plb500/AutoBloomer-SensorModule/hardware/HIB/PCB/HardwareInterfaceBoard.kicad_sch

## KiCad design hardware/HIB/PCB/HardwareInterfaceBoard.kicad_sch (2024-02-22)

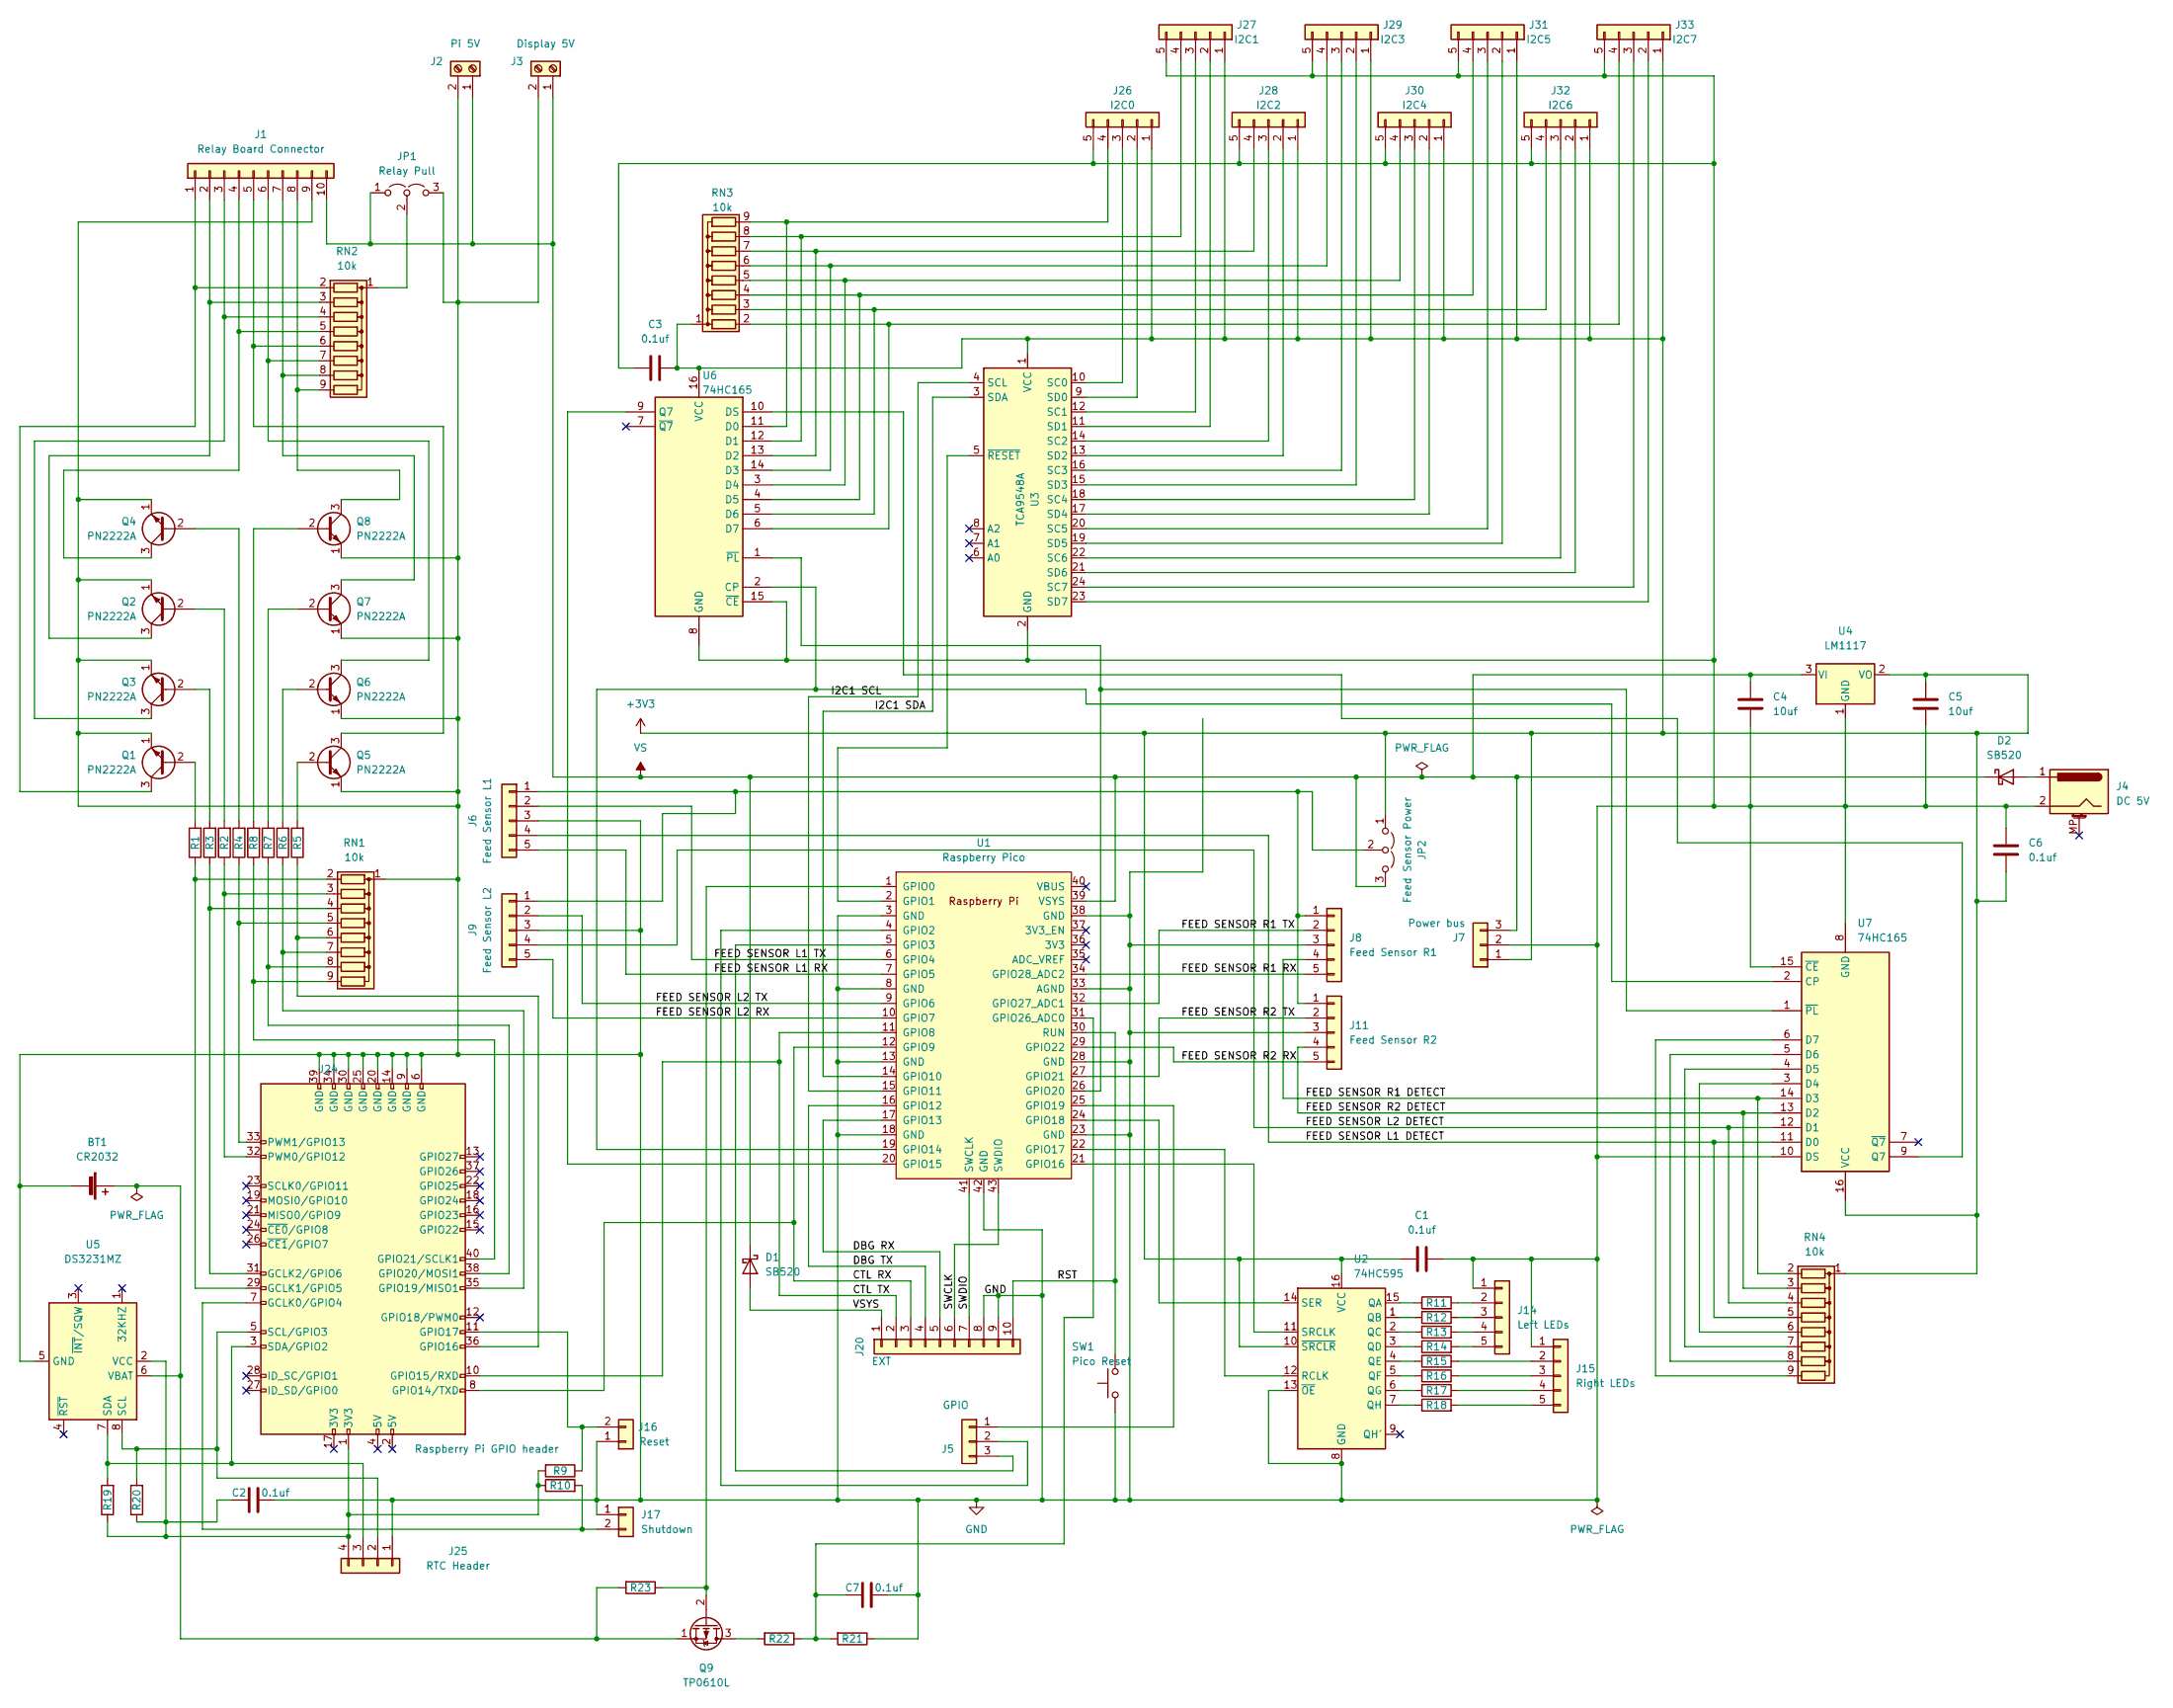
[picture p12: schematic HardwareInterfaceBoard.kicad_sch]

Parts:
BT1: CR2032; BatteryHolder_Keystone_1058_1x2032
C1, C2, C3, C6, C7: 0.1uf; C_Disc_D6.0mm_W2.5mm_P5.00mm
C4, C5: 10uf; C_Disc_D6.0mm_W2.5mm_P5.00mm
D1, D2: SB520; D_DO-201AD_P15.24mm_Horizontal
J1: Relay Board Connector; JST_XH_B10B-XH-A_1x10_P2.50mm_Vertical
J2: Pi 5V; JST_XH_B2B-XH-A_1x02_P2.50mm_Vertical
J3: Display 5V; JST_XH_B2B-XH-A_1x02_P2.50mm_Vertical
J4: DC 5V; BarrelJack_Horizontal_MP
J5: GPIO; PinHeader_1x03_P2.54mm_Vertical
J6: Feed Sensor L1; JST_XH_B5B-XH-A_1x05_P2.50mm_Vertical
J7: Power bus; PinHeader_1x03_P2.54mm_Vertical
J8: Feed Sensor R1; JST_XH_B5B-XH-A_1x05_P2.50mm_Vertical
J9: Feed Sensor L2; JST_XH_B5B-XH-A_1x05_P2.50mm_Vertical
J11: Feed Sensor R2; JST_XH_B5B-XH-A_1x05_P2.50mm_Vertical
J14: Left LEDs; JST_XH_B5B-XH-A_1x05_P2.50mm_Vertical
J15: Right LEDs; JST_XH_B5B-XH-A_1x05_P2.50mm_Vertical
J16: Reset; JST_XH_B2B-XH-A_1x02_P2.50mm_Vertical
J17: Shutdown; JST_XH_B2B-XH-A_1x02_P2.50mm_Vertical
J20: EXT; JST_XH_B10B-XH-A_1x10_P2.50mm_Vertical
J24: Raspberry Pi GPIO header; PinHeader_2x20_P2.54mm_Vertical
J25: RTC Header; PinHeader_1x04_P2.54mm_Vertical
J26: I2C0; JST_XH_B5B-XH-A_1x05_P2.50mm_Vertical
J27: I2C1; JST_XH_B5B-XH-A_1x05_P2.50mm_Vertical
J28: I2C2; JST_XH_B5B-XH-A_1x05_P2.50mm_Vertical
J29: I2C3; JST_XH_B5B-XH-A_1x05_P2.50mm_Vertical
J30: I2C4; JST_XH_B5B-XH-A_1x05_P2.50mm_Vertical
J31: I2C5; JST_XH_B5B-XH-A_1x05_P2.50mm_Vertical
J32: I2C6; JST_XH_B5B-XH-A_1x05_P2.50mm_Vertical
J33: I2C7; JST_XH_B5B-XH-A_1x05_P2.50mm_Vertical
JP1: Relay Pull; PinHeader_1x03_P2.54mm_Vertical
JP2: Feed Sensor Power; PinHeader_1x03_P2.54mm_Vertical
Q1, Q2, Q3, Q4, Q5, Q6, Q7, Q8: PN2222A; TO-92_Inline
Q9: TP0610L; TO-92_Inline
R1, R2, R3, R4, R5, R6, R7, R8: 2.2k; R_Axial_DIN0207_L6.3mm_D2.5mm_P7.62mm_Horizontal
R9, R10: 10k; R_Axial_DIN0207_L6.3mm_D2.5mm_P7.62mm_Horizontal
R11, R12, R13, R14, R15, R16, R17, R18: 300; R_Axial_DIN0207_L6.3mm_D2.5mm_P7.62mm_Horizontal
R19, R20: 4.3k; R_Axial_DIN0207_L6.3mm_D2.5mm_P7.62mm_Horizontal
R21, R22, R23: 100k; R_Axial_DIN0207_L6.3mm_D2.5mm_P7.62mm_Horizontal
RN1, RN2, RN3, RN4: 10k; R_Array_SIP9
SW1: Pico Reset; SW_PUSH_6mm
U1: Raspberry Pico; RPi_PicoW_SMD_TH
U2: 74HC595; DIP-16_W7.62mm
U3: TCA9548A; DIP-24_W15.24mm
U4: LM1117; TO-220-3_Horizontal_TabDown
U5: DS3231MZ; SOIC-8_3.9x4.9mm_P1.27mm
U6, U7: 74HC165; DIP-16_W7.62mm

Connections:
+3V3: C1.1, C3.1, C5.1, C6.2, J7.1, J26.1, J27.1, J28.1, J29.1, J30.1, J31.1, J32.1, J33.1, JP2.1 (A), RN3.1 (common), RN4.1 (common), U2.10 (~SRCLR), U2.16 (VCC), U3.1 (VCC), U4.2 (VO), U6.16 (VCC), U7.16 (VCC)
CTL RX: J20.3, J24.8 (GPIO14/TXD), U1.12 (GPIO9)
CTL TX: J20.2, J24.10 (GPIO15/RXD), U1.11 (GPIO8)
DBG RX: J20.5, U1.17 (GPIO13)
DBG TX: J20.4, U1.16 (GPIO12)
FEED SENSOR L1 DETECT: J6.4, RN4.5 (R4), U7.11 (D0)
FEED SENSOR L1 RX: J6.5, U1.7 (GPIO5)
FEED SENSOR L1 TX: J6.2, U1.6 (GPIO4)
FEED SENSOR L2 DETECT: J9.4, RN4.4 (R3), U7.12 (D1)
FEED SENSOR L2 RX: J9.5, U1.10 (GPIO7)
FEED SENSOR L2 TX: J9.2, U1.9 (GPIO6)
FEED SENSOR R1 DETECT: J8.4, RN4.2 (R1), U7.14 (D3)
FEED SENSOR R1 RX: J8.5, U1.34 (GPIO28_ADC2)
FEED SENSOR R1 TX: J8.2, U1.32 (GPIO27_ADC1)
FEED SENSOR R2 DETECT: J11.4, RN4.3 (R2), U7.13 (D2)
FEED SENSOR R2 RX: J11.5, U1.29 (GPIO22)
FEED SENSOR R2 TX: J11.2, U1.27 (GPIO21)
GND: BT1.2 (-), C1.2, C2.2, C3.2, C4.1, C5.2, C6.1, C7.2, J1.9, J2.2, J3.2, J4.2, J6.3, J7.2, J8.3, J9.3, J11.3, J14.1, J15.1, J16.1, J17.1, J20.8, J20.9, J24.6 (GND), J24.9 (GND), J24.14 (GND), J24.20 (GND), J24.25 (GND), J24.30 (GND), J24.34 (GND), J24.39 (GND), J25.1, J26.5, J27.5, J28.5, J29.5, J30.5, J31.5, J32.5, J33.5, JP1.3 (B), Q1.1 (E), Q2.1 (E), Q3.1 (E), Q4.1 (E), Q5.1 (E), Q6.1 (E), Q7.1 (E), Q8.1 (E), R21.1, RN1.1 (common), SW1.1, U1.3 (GND), U1.8 (GND), U1.13 (GND), U1.18 (GND), U1.23 (GND), U1.28 (GND), U1.33 (AGND), U1.38 (GND), U1.42 (GND), U2.8 (GND), U2.13 (~OE), U3.2 (GND), U4.1 (GND), U5.5 (GND), U6.8 (GND), U6.15 (~CE), U7.8 (GND), U7.10 (DS), U7.15 (~CE)
I2C1 SCL: U1.15 (GPIO11), U3.4 (SCL)
I2C1 SDA: U1.14 (GPIO10), U3.3 (SDA)
unnamed: BT1.1 (+), Q9.1 (S), R23.2, U5.6 (VBAT)
unnamed: C2.1, J24.1 (3V3), J25.4, R9.2, R10.1, R19.1, R20.1, U5.2 (VCC)
unnamed: C7.1, R21.2, R22.1, U1.31 (GPIO26_ADC0)
unnamed: D2.2 (A), J4.1
unnamed: J1.1, Q1.3 (C), RN2.2 (R1)
unnamed: J1.2, Q2.3 (C), RN2.3 (R2)
unnamed: J1.3, Q3.3 (C), RN2.4 (R3)
unnamed: J1.4, Q4.3 (C), RN2.5 (R4)
unnamed: J1.5, Q5.3 (C), RN2.6 (R5)
unnamed: J1.6, Q6.3 (C), RN2.7 (R6)
unnamed: J1.7, Q7.3 (C), RN2.8 (R7)
unnamed: J1.8, Q8.3 (C), RN2.9 (R8)
unnamed: J5.1, U1.25 (GPIO19)
unnamed: J5.2, U1.4 (GPIO2)
unnamed: J5.3, U1.5 (GPIO3)
unnamed: J6.1, J8.1, J9.1, J11.1, JP2.2 (C)
unnamed: J14.2, R11.2
unnamed: J14.3, R12.2
unnamed: J14.4, R13.2
unnamed: J14.5, R14.2
unnamed: J15.2, R15.2
unnamed: J15.3, R16.2
unnamed: J15.4, R17.2
unnamed: J15.5, R18.2
unnamed: J16.2, J24.11 (GPIO17), R9.1
unnamed: J17.2, J24.7 (GCLK0/GPIO4), R10.2
unnamed: J24.3 (SDA/GPIO2), J25.3, R19.2, U5.7 (SDA)
unnamed: J24.5 (SCL/GPIO3), J25.2, R20.2, U5.8 (SCL)
unnamed: J24.29 (GCLK1/GPIO5), R1.1, RN1.2 (R1)
unnamed: J24.31 (GCLK2/GPIO6), R3.1, RN1.4 (R3)
unnamed: J24.32 (PWM0/GPIO12), R2.1, RN1.3 (R2)
unnamed: J24.33 (PWM1/GPIO13), R4.1, RN1.5 (R4)
unnamed: J24.35 (GPIO19/MISO1), R6.1, RN1.7 (R6)
unnamed: J24.36 (GPIO16), R5.1, RN1.6 (R5)
unnamed: J24.38 (GPIO20/MOSI1), R7.1, RN1.8 (R7)
unnamed: J24.40 (GPIO21/SCLK1), R8.1, RN1.9 (R8)
unnamed: J26.2, U3.9 (SD0)
unnamed: J26.3, U3.10 (SC0)
unnamed: J26.4, RN3.9 (R8), U6.11 (D0)
unnamed: J27.2, U3.11 (SD1)
unnamed: J27.3, U3.12 (SC1)
unnamed: J27.4, RN3.8 (R7), U6.12 (D1)
unnamed: J28.2, U3.13 (SD2)
unnamed: J28.3, U3.14 (SC2)
unnamed: J28.4, RN3.7 (R6), U6.13 (D2)
unnamed: J29.2, U3.15 (SD3)
unnamed: J29.3, U3.16 (SC3)
unnamed: J29.4, RN3.6 (R5), U6.14 (D3)
unnamed: J30.2, U3.17 (SD4)
unnamed: J30.3, U3.18 (SC4)
unnamed: J30.4, RN3.5 (R4), U6.3 (D4)
unnamed: J31.2, U3.19 (SD5)
unnamed: J31.3, U3.20 (SC5)
unnamed: J31.4, RN3.4 (R3), U6.4 (D5)
unnamed: J32.2, U3.21 (SD6)
unnamed: J32.3, U3.22 (SC6)
unnamed: J32.4, RN3.3 (R2), U6.5 (D6)
unnamed: J33.2, U3.23 (SD7)
unnamed: J33.3, U3.24 (SC7)
unnamed: J33.4, RN3.2 (R1), U6.6 (D7)
unnamed: JP1.2 (C), RN2.1 (common)
unnamed: Q1.2 (B), R1.2
unnamed: Q2.2 (B), R2.2
unnamed: Q3.2 (B), R3.2
unnamed: Q4.2 (B), R4.2
unnamed: Q5.2 (B), R5.2
unnamed: Q6.2 (B), R6.2
unnamed: Q7.2 (B), R7.2
unnamed: Q8.2 (B), R8.2
unnamed: Q9.2 (G), R23.1, U1.1 (GPIO0)
unnamed: Q9.3 (D), R22.2
unnamed: R11.1, U2.15 (QA)
unnamed: R12.1, U2.1 (QB)
unnamed: R13.1, U2.2 (QC)
unnamed: R14.1, U2.3 (QD)
unnamed: R15.1, U2.4 (QE)
unnamed: R16.1, U2.5 (QF)
unnamed: R17.1, U2.6 (QG)
unnamed: R18.1, U2.7 (QH)
unnamed: RN4.6 (R5), U7.3 (D4)
unnamed: RN4.7 (R6), U7.4 (D5)
unnamed: RN4.8 (R7), U7.5 (D6)
unnamed: RN4.9 (R8), U7.6 (D7)
unnamed: U1.2 (GPIO1), U3.5 (~RESET)
unnamed: U1.19 (GPIO14), U6.2 (CP), U7.2 (CP)
unnamed: U1.20 (GPIO15), U6.9 (Q7)
unnamed: U1.21 (GPIO16), U2.11 (SRCLK)
unnamed: U1.22 (GPIO17), U2.12 (RCLK)
unnamed: U1.24 (GPIO18), U2.14 (SER)
unnamed: U1.26 (GPIO20), U6.1 (~PL), U7.1 (~PL)
unnamed: U6.10 (DS), U7.9 (Q7)
RST: J20.10, SW1.2, U1.30 (RUN)
SWCLK: J20.6, U1.43 (SWDIO)
SWDIO: J20.7, U1.41 (SWCLK)
VS: C4.2, D1.1 (K), D2.1 (K), J1.10, J2.1, J3.1, J7.3, JP1.1 (A), JP2.3 (B), U1.39 (VSYS), U4.3 (VI)
VSYS: D1.2 (A), J20.1
