plb500/AutoBloomer-SensorModule/pico/src/sensors/sensor_types/stemma_soil_sensor.cpp

#include "stemma_soil_sensor.h"

#include "util/debug_io.h"

#include <tuple>
#include <cstring>
#include <cstdio>


using std::make_tuple;

const uint8_t SEESAW_STATUS_BASE                = 0x00;
const uint8_t SEESAW_STATUS_HW_ID               = 0x01;
const uint8_t SEESAW_STATUS_SWRST               = 0x7F;
const uint8_t SEESAW_HW_ID_CODE                 = 0x55;
const uint8_t SEESAW_STATUS_VERSION             = 0x02;
const uint8_t SEESAW_TOUCH_BASE                 = 0x0F;
const uint8_t SEESAW_TOUCH_CHANNEL_OFFSET       = 0x10;

constexpr const char* SOIL_MOISTURE_JSON_KEY    = "SoilMoisture";


StemmaSoilSensor::StemmaSoilSensor(I2CInterface& i2cInterface, uint8_t address) :
    Sensor(Sensor::STEMMA_SOIL_SENSOR, &StemmaSoilSensor::serializeDataToJSON),
    mI2CInterface(i2cInterface),
    mAddress(address),
    mActive(false)
{}

void StemmaSoilSensor::doInitialization() {
    mI2CInterface.initSensorBus();

    uint8_t response = 0x33;
    mActive = false;

    // Scan bus for device at given address
    bool found = false;
    for (int retries = 0; retries < 10; retries++) {
        if(mI2CInterface.checkI2CAddress(mAddress) == I2C_RESPONSE_OK) {
            found = true;
            break;
        }
        sleep_ms(2);
    }

    if (!found) {
        return;
    }

    // Reset device
    found = false;
    for (int retries = 0; retries < 10; retries++) {
        if(mI2CInterface.checkI2CAddress(mAddress) == I2C_RESPONSE_OK) {
            found = true;
            break;
        }
        sleep_ms(2);
    }

    if (!found) {
        return;
    } else {
        reset();
    }

    sleep_ms(2);

    // Get hardware ID from device
    found = false;
    for (int retries = 0; !found && retries < 10; retries++) {
        mI2CInterface.readFromI2CRegister(mAddress,  SEESAW_STATUS_BASE, SEESAW_STATUS_HW_ID, &response, 1, 4);

        if(response == SEESAW_HW_ID_CODE) {
            found = true;
            break;
        }
    }

    mActive = (getVersion() != STEMMA_SOIL_SENSOR_INVALID_READING);
}

void StemmaSoilSensor::reset() {
    const uint8_t resetBuffer[] = {
        0xFF
    };

    mI2CInterface.writeToI2CRegister(mAddress, SEESAW_STATUS_BASE, SEESAW_STATUS_SWRST, resetBuffer, 1);
}

void StemmaSoilSensor::shutdown() {
    mI2CInterface.shutdownSensorBus();
}

int StemmaSoilSensor::serializeDataToJSON(uint8_t* data, uint8_t dataSize, char* jsonBuffer, int jsonBufferSize) {
    uint16_t moisture;
    memcpy(&moisture, data, sizeof(uint16_t));

    return snprintf(jsonBuffer, jsonBufferSize,
        "\"%s\": %d",
        SOIL_MOISTURE_JSON_KEY, moisture
    );
}

Sensor::SensorUpdateResponse StemmaSoilSensor::doUpdate(absolute_time_t currentTime, uint8_t *dataStorageBuffer, size_t bufferSize) {
    if(!mActive) {
        return make_tuple(SENSOR_INACTIVE, 0);
    }

    uint16_t capValue = getCapacitiveValue();
    if(capValue != StemmaSoilSensor::STEMMA_SOIL_SENSOR_INVALID_READING) {
        DEBUG_PRINT(1, "+--------------------------------+");
        DEBUG_PRINT(1, "|      Stemma Soil Sensor        |");
        DEBUG_PRINT(1, "| Soil moisture: %4d            |", capValue);
        DEBUG_PRINT(1, "+--------------------------------+\n");

        memcpy(dataStorageBuffer, &capValue, sizeof(uint16_t));
        return make_tuple(SENSOR_OK, sizeof(uint16_t));
    } else {
        // Got an invalid reading, might be something up with the port
        DEBUG_PRINT(1, "+--------------------------------+");
        DEBUG_PRINT(1, "|      Stemma Soil Sensor        |");
        DEBUG_PRINT(1, "|       * MALFUNCTION *          |", capValue);
        DEBUG_PRINT(1, "+--------------------------------+\n");
        return make_tuple(SENSOR_MALFUNCTIONING, 0);
    }

    // No idea how we got here, but it's not good
    return make_tuple(SENSOR_MALFUNCTIONING, 0);
}

uint32_t StemmaSoilSensor::getVersion() {
    uint8_t buf[4];

    if(mI2CInterface.readFromI2CRegister(
        mAddress, 
        SEESAW_STATUS_BASE,
        SEESAW_STATUS_VERSION, 
        buf,
        4,
        100
    ) != I2C_RESPONSE_OK) {
        return STEMMA_SOIL_SENSOR_INVALID_READING;
    }

    return (((uint) buf[0] << 24) | 
            ((uint) buf[1] << 16) |
            ((uint) buf[2] << 8) |
            (uint) buf[3]);
}

uint16_t StemmaSoilSensor::getCapacitiveValue() {
    static const uint16_t READ_DELAY_MS = 5;
    static const uint16_t NUM_RETRIES = 3;
    static const int READING_BUFFER_SIZE = 2;
    
    uint8_t buf[READING_BUFFER_SIZE];
    uint16_t ret = STEMMA_SOIL_SENSOR_INVALID_READING;

    for(uint8_t retry = 0; retry < NUM_RETRIES; retry++) {
        if(mI2CInterface.readFromI2CRegister(
            mAddress,
            SEESAW_TOUCH_BASE, 
            SEESAW_TOUCH_CHANNEL_OFFSET, 
            buf, 
            READING_BUFFER_SIZE, 
            READ_DELAY_MS
        ) == I2C_RESPONSE_OK) {
            ret = ((uint16_t) buf[0] << 8) | buf[1];

            if(ret < CAPACITIVE_READING_MIN) {
                ret = CAPACITIVE_READING_MIN;
            } else if(ret > CAPACITIVE_READING_MAX) {
                ret = CAPACITIVE_READING_MAX;
            }

            ret = ((ret - CAPACITIVE_READING_MIN) * 100) / (CAPACITIVE_READING_MAX - CAPACITIVE_READING_MIN);
        }
    }
    return ret;
}
