plb500/AutoBloomer-SensorModule/pico/src/sensors/sensor_types/sonar_sensor.h

#ifndef _SONAR_SENSOR_H_
#define _SONAR_SENSOR_H_

#include "sensors/sensor.h"
#include "hardware/pio.h"
#include "board_hardware/connection_io.h"


struct PIOWrapper {
    PIO mPIO;
    uint mOffset;
    bool mInitialized;
};

class SonarSensor : public Sensor {
    public:
        SonarSensor(
            PIOWrapper &pioWrapper, int stateMachineID, int txPin, int rxPin, int baud, ConnectionIO& connectionIO);

        virtual void reset();
        virtual void shutdown();                

        virtual constexpr uint16_t getRawDataSize() const { return RAW_DATA_SIZE; }
        
        static int serializeDataToJSON(uint8_t* data, uint8_t dataSize, char* jsonBuffer, int jsonBufferSize);

        static const uint32_t RAW_DATA_SIZE = sizeof(uint16_t);

    protected:
        virtual void doInitialization();
        virtual SensorUpdateResponse doUpdate(absolute_time_t currentTime, uint8_t *dataStorageBuffer, size_t bufferSize);

    private:
        static void initializeSonarPIO(PIOWrapper& pioWrapper);

        static constexpr int SONAR_SENSOR_PACKET_SIZE   = 4;

        PIOWrapper& mPIOWrapper;
        const uint mStateMachineID;
        const int mTXPin;
        const int mRXPin;
        const int mBaudrate;
        ConnectionIO& mConnectionIO;

        char mPacketBuffer[SONAR_SENSOR_PACKET_SIZE];
        int mCurrentBufferPos;
};

#endif      // _SONAR_SENSOR_H
