plb500/AutoBloomer-SensorModule/pico/src/sensors/sensor_types/dummy_sensor.h

#ifndef _DUMMY_SENSOR_H_
#define _DUMMY_SENSOR_H_

#include "sensors/sensor.h"

class DummySensor : public Sensor {
    public:
        DummySensor();

        virtual void reset() {}
        virtual void shutdown() {}

        virtual constexpr uint16_t getRawDataSize() const { 
            return sizeof(int) + sizeof(float);
        }

        static int serializeDataToJSON(uint8_t* data, uint8_t dataSize, char* jsonBuffer, int jsonBufferSize);
        virtual bool handleSensorControlCommand(SensorControlMessage& message);

        static const uint32_t RAW_DATA_SIZE = (sizeof(int) + sizeof(float));
    protected:
        virtual void doInitialization() {}
        Sensor::SensorUpdateResponse doUpdate(absolute_time_t currentTime, uint8_t *dataStorageBuffer, size_t bufferSize);

    private:
        static constexpr int UPDATE_TIME_MS     = 2000;

        int mDummyInt;
        float mDummyFloat;
        absolute_time_t mNextUpdateTime;
};

#endif      // _DUMMY_SENSOR_H_
