plb500/AutoBloomer-SensorModule/pico/src/sensors/hardware_interfaces/sensirion/bitbang/sensirion_sw_i2c_hal.c

/*
 * Copyright (c) 2018, Sensirion AG
 * All rights reserved.
 *
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
 * * Neither the name of Sensirion AG nor the names of its
 *   contributors may be used to endorse or promote products derived from
 *   this software without specific prior written permission.
 *
 * THIS SOFTWARE IS PROVIDED BY THE COPYRIGHT HOLDERS AND CONTRIBUTORS "AS IS"
 * AND ANY EXPRESS OR IMPLIED WARRANTIES, INCLUDING, BUT NOT LIMITED TO, THE
 * IMPLIED WARRANTIES OF MERCHANTABILITY AND FITNESS FOR A PARTICULAR PURPOSE
 * ARE DISCLAIMED. IN NO EVENT SHALL THE COPYRIGHT HOLDER OR CONTRIBUTORS BE
 * LIABLE FOR ANY DIRECT, INDIRECT, INCIDENTAL, SPECIAL, EXEMPLARY, OR
 * CONSEQUENTIAL DAMAGES (INCLUDING, BUT NOT LIMITED TO, PROCUREMENT OF
 * SUBSTITUTE GOODS OR SERVICES; LOSS OF USE, DATA, OR PROFITS; OR BUSINESS
 * INTERRUPTION) HOWEVER CAUSED AND ON ANY THEORY OF LIABILITY, WHETHER IN
 * CONTRACT, STRICT LIABILITY, OR TORT (INCLUDING NEGLIGENCE OR OTHERWISE)
 * ARISING IN ANY WAY OUT OF THE USE OF THIS SOFTWARE, EVEN IF ADVISED OF THE
 * POSSIBILITY OF SUCH DAMAGE.
 */

#include "sensors/hardware_interfaces/sensirion/common/sensirion_config.h"
#include "sensors/hardware_interfaces/sensirion/common/sensirion_common.h"
#include "sensors/hardware_interfaces/sensirion/common/sensirion_i2c.h"
#include "sensirion_sw_i2c_gpio.h"
#include "sensors/hardware_interfaces/sensor_i2c_interface.h"
#include "util/debug_io.h"
#include "pico/time.h"

#define DELAY_USEC (SENSIRION_I2C_CLOCK_PERIOD_USEC / 2)

I2CInterface* _I2C_INTERFACE = 0;

void sensirion_i2c_hal_sleep_usec(uint32_t useconds) {
    sleep_us(useconds);
}

static int8_t sensirion_wait_while_clock_stretching(void) {
    /* Maximal timeout of 150ms (SCD30) in sleep polling cycles */
    uint32_t timeout_cycles = 150000 / SENSIRION_I2C_CLOCK_PERIOD_USEC;

    while (--timeout_cycles) {
        if (sensirion_SCL_read(_I2C_INTERFACE))
            return NO_ERROR;
        sensirion_sleep_usec(SENSIRION_I2C_CLOCK_PERIOD_USEC);
    }

    return STATUS_FAIL;
}

static int8_t sensirion_i2c_write_byte(uint8_t data) {
    int8_t nack, i;
    for (i = 7; i >= 0; i--) {
        sensirion_SCL_out(_I2C_INTERFACE);
        if ((data >> i) & 0x01)
            sensirion_SDA_in(_I2C_INTERFACE);
        else
            sensirion_SDA_out(_I2C_INTERFACE);
        sensirion_sleep_usec(DELAY_USEC);
        sensirion_SCL_in(_I2C_INTERFACE);
        sensirion_sleep_usec(DELAY_USEC);
        if (sensirion_wait_while_clock_stretching())
            return STATUS_FAIL;
    }
    sensirion_SCL_out(_I2C_INTERFACE);
    sensirion_SDA_in(_I2C_INTERFACE);
    sensirion_sleep_usec(DELAY_USEC);
    sensirion_SCL_in(_I2C_INTERFACE);
    if (sensirion_wait_while_clock_stretching())
        return STATUS_FAIL;
    nack = (sensirion_SDA_read(_I2C_INTERFACE) != 0);
    sensirion_SCL_out(_I2C_INTERFACE);

    return nack;
}

static uint8_t sensirion_i2c_read_byte(uint8_t ack) {
    int8_t i;
    uint8_t data = 0;
    sensirion_SDA_in(_I2C_INTERFACE);
    for (i = 7; i >= 0; i--) {
        sensirion_sleep_usec(DELAY_USEC);
        sensirion_SCL_in(_I2C_INTERFACE);
        if (sensirion_wait_while_clock_stretching())
            return 0xFF;  // return 0xFF on error
        data |= (sensirion_SDA_read(_I2C_INTERFACE) != 0) << i;
        sensirion_SCL_out(_I2C_INTERFACE);
    }
    if (ack)
        sensirion_SDA_out(_I2C_INTERFACE);
    else
        sensirion_SDA_in(_I2C_INTERFACE);
    sensirion_sleep_usec(DELAY_USEC);
    sensirion_SCL_in(_I2C_INTERFACE);
    sensirion_sleep_usec(DELAY_USEC);
    if (sensirion_wait_while_clock_stretching())
        return 0xFF;  // return 0xFF on error
    sensirion_SCL_out(_I2C_INTERFACE);
    sensirion_SDA_in(_I2C_INTERFACE);

    return data;
}

static int8_t sensirion_i2c_start(void) {
    sensirion_SCL_in(_I2C_INTERFACE);
    if (sensirion_wait_while_clock_stretching())
        return STATUS_FAIL;

    sensirion_SDA_out(_I2C_INTERFACE);
    sensirion_sleep_usec(DELAY_USEC);
    sensirion_SCL_out(_I2C_INTERFACE);
    sensirion_sleep_usec(DELAY_USEC);
    return NO_ERROR;
}

static void sensirion_i2c_stop(void) {
    sensirion_SDA_out(_I2C_INTERFACE);
    sensirion_sleep_usec(DELAY_USEC);
    sensirion_SCL_in(_I2C_INTERFACE);
    sensirion_sleep_usec(DELAY_USEC);
    sensirion_SDA_in(_I2C_INTERFACE);
    sensirion_sleep_usec(DELAY_USEC);
}

int8_t sensirion_i2c_hal_write(uint8_t address, const uint8_t* data,
                           uint16_t count) {
    int8_t ret;
    uint16_t i;

    ret = sensirion_i2c_start();
    if (ret != NO_ERROR)
        return ret;

    ret = sensirion_i2c_write_byte(address << 1);
    if (ret != NO_ERROR) {
        sensirion_i2c_stop();
        return ret;
    }

    for (i = 0; i < count; i++) {
        ret = sensirion_i2c_write_byte(data[i]);
        if (ret != NO_ERROR) {
            sensirion_i2c_stop();
            break;
        }
    }
    sensirion_i2c_stop();
    return ret;
}

int8_t sensirion_i2c_hal_read(uint8_t address, uint8_t* data, uint16_t count) {
    int8_t ret;
    uint8_t send_ack;
    uint16_t i;

    ret = sensirion_i2c_start();
    if (ret != NO_ERROR)
        return ret;

    ret = sensirion_i2c_write_byte((address << 1) | 1);
    if (ret != NO_ERROR) {
        sensirion_i2c_stop();
        return ret;
    }

    for (i = 0; i < count; i++) {
        send_ack = i < (count - 1); /* last byte must be NACK'ed */
        data[i] = sensirion_i2c_read_byte(send_ack);
    }

    sensirion_i2c_stop();
    return NO_ERROR;
}

void sensirion_i2c_hal_init(I2CInterface* i2c) {
    assert(i2c);

    _I2C_INTERFACE = i2c;

    sensirion_init_pins(_I2C_INTERFACE);
    sensirion_SCL_in(_I2C_INTERFACE);
    sensirion_SDA_in(_I2C_INTERFACE);
}

void sensirion_i2c_hal_free(void) {
    assert(_I2C_INTERFACE);

    sensirion_SCL_in(_I2C_INTERFACE);
    sensirion_SDA_in(_I2C_INTERFACE);
    sensirion_release_pins(_I2C_INTERFACE);

    _I2C_INTERFACE = 0;
}
